andilge/8ch-constant-current-LED-driver/images/buck_converter.jpg

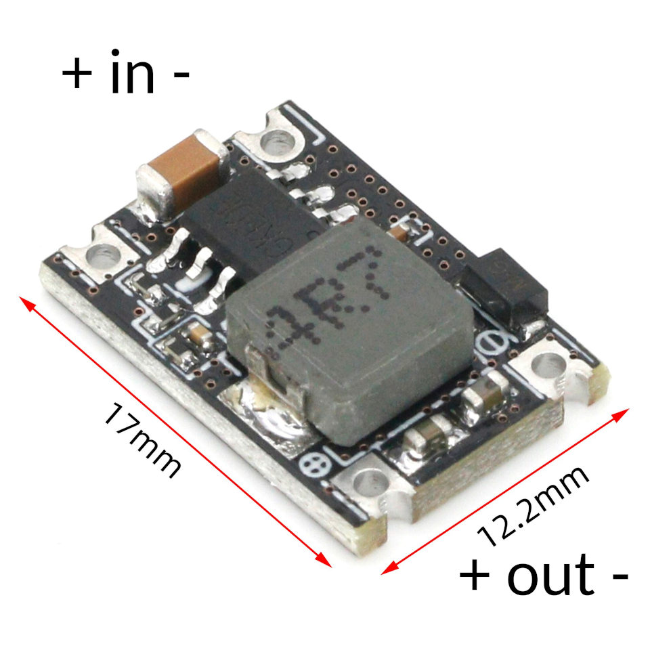
images/buck_converter.jpg
