andilge/8ch-constant-current-LED-driver/images/real-board-front.jpg

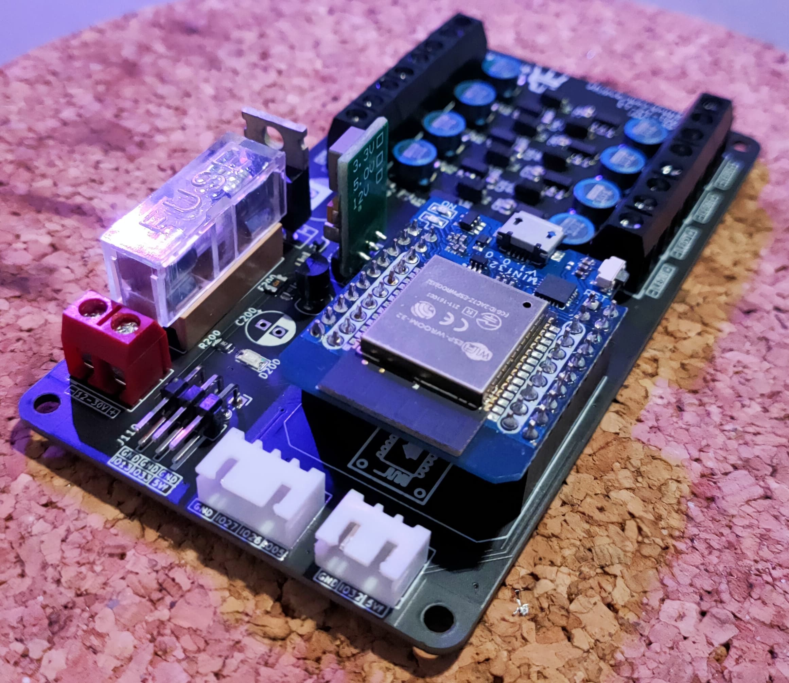
images/real-board-front.jpg
