andilge/8ch-constant-current-LED-driver/revisions/2022-01-15/board-views/front.png

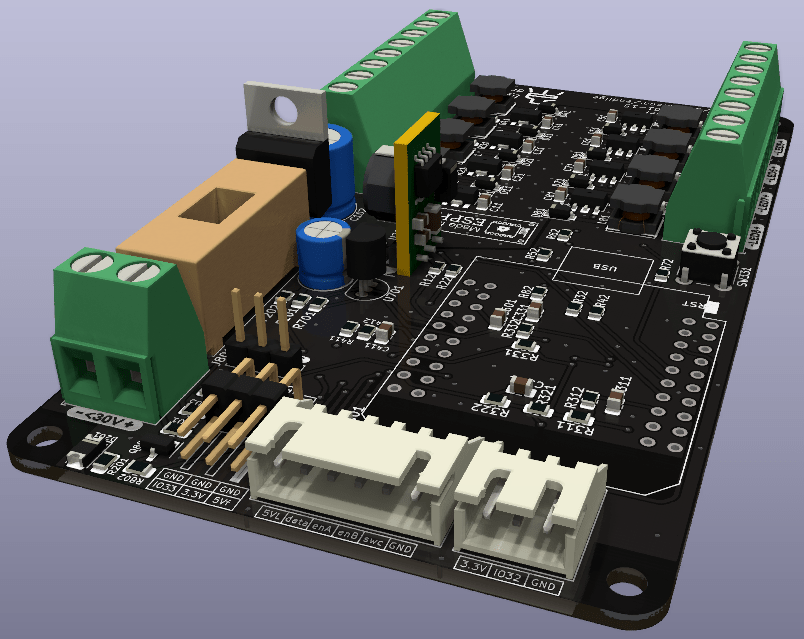
revisions/2022-01-15/board-views/front.png
