andilge/8ch-constant-current-LED-driver/revisions/2022-01-15/board-views/rear.png

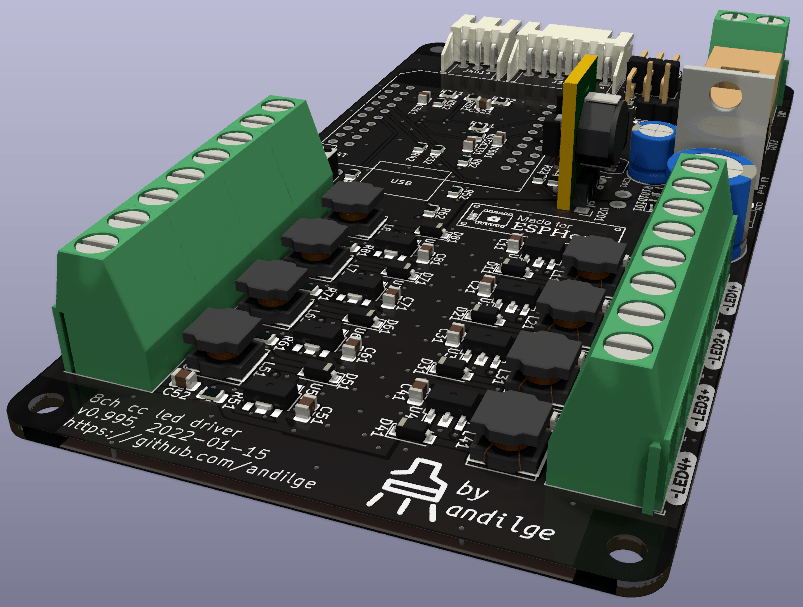
revisions/2022-01-15/board-views/rear.png
