andilge/8ch-constant-current-LED-driver/revisions/2022-01-15/board-views/right-real.jpg

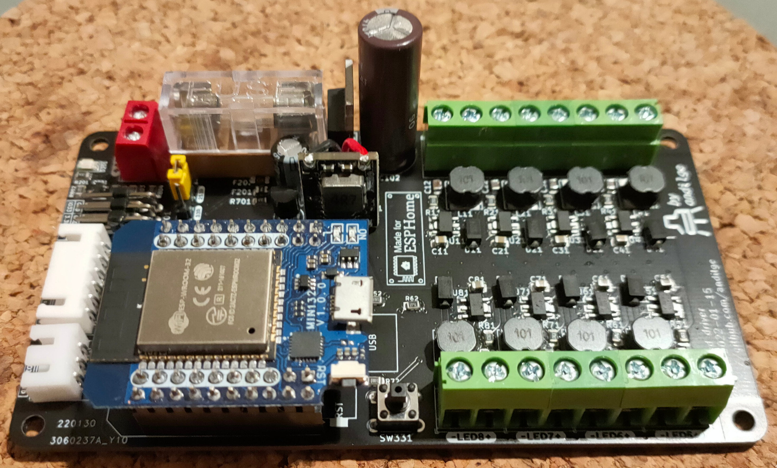
revisions/2022-01-15/board-views/right-real.jpg
