andilge/8ch-constant-current-LED-driver/revisions/2022-03-28/board-views/right.png

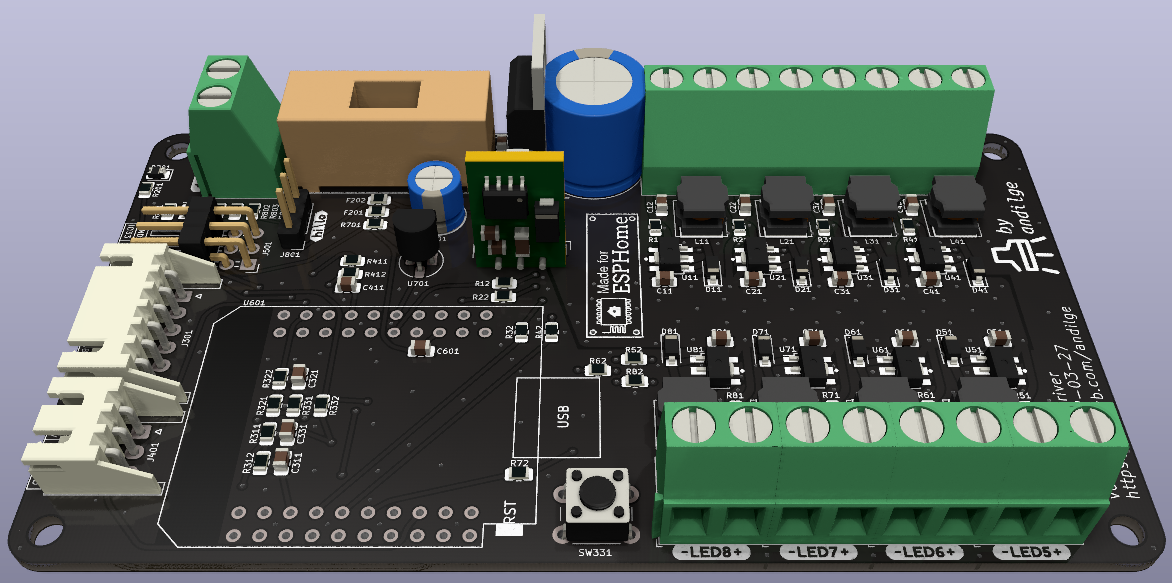
revisions/2022-03-28/board-views/right.png
