andilge/8ch-constant-current-LED-driver/revisions/dimension-charts/mounting-hole-distance-board-y.png

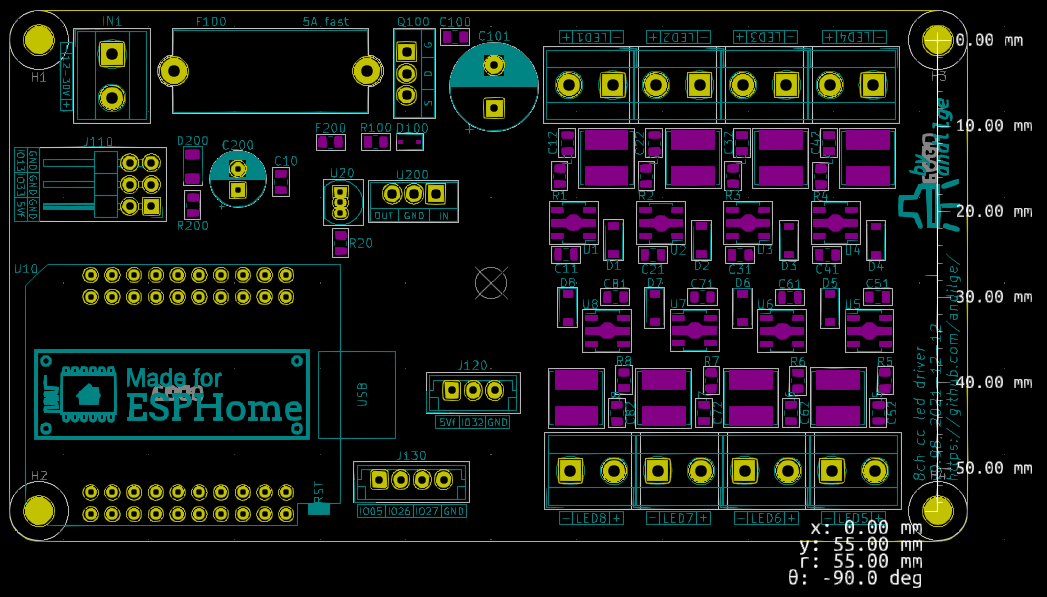
revisions/dimension-charts/mounting-hole-distance-board-y.png
