andilge/8ch-constant-current-LED-driver/revisions/dimension-charts/mounting-hole-distances-box.png

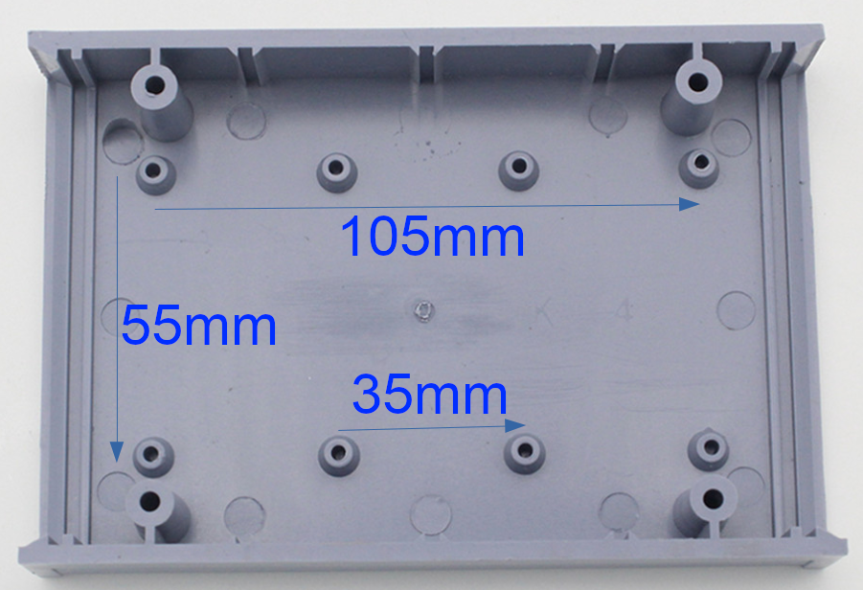
revisions/dimension-charts/mounting-hole-distances-box.png
