andilge/8ch-constant-current-LED-driver/revisions/dimension-charts/outer-dimension-board-y.png

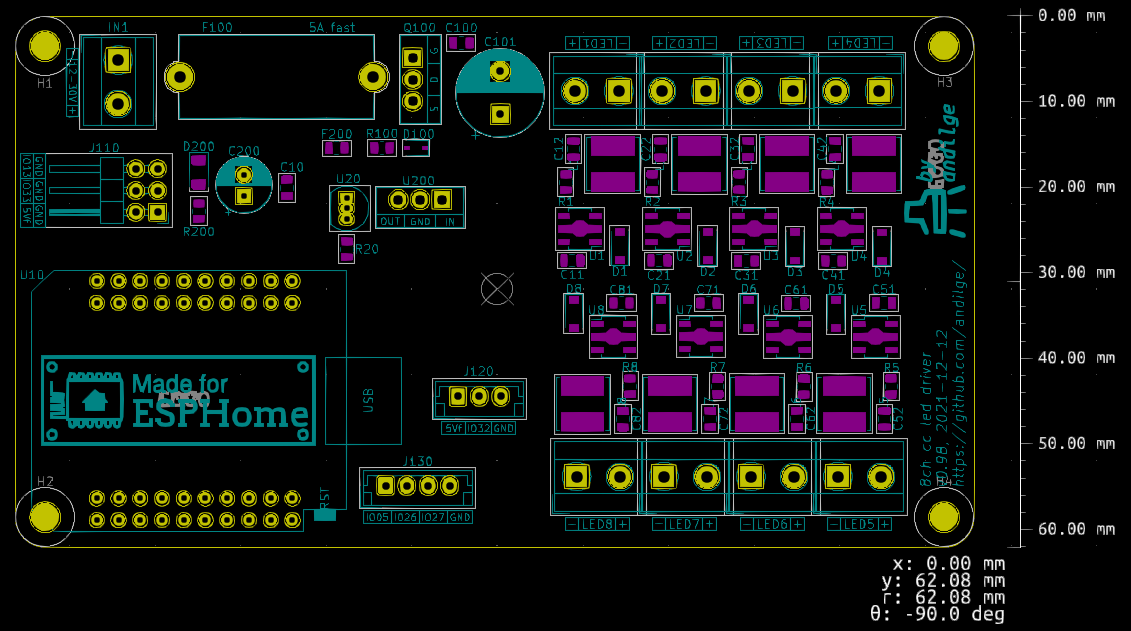
revisions/dimension-charts/outer-dimension-board-y.png
